TheVizWiz/ESP32-Drone/Controller/Controller Code/src/main.h

//
// Created by vibhu on 6/9/2022.
//

#ifndef CONTROLLER_CODE_MAIN_H
#define CONTROLLER_CODE_MAIN_H

#include <AsyncWebSocket.h>

void parseInput ();

void writeJSON ();

#endif //CONTROLLER_CODE_MAIN_H
